fredriknk/ssense/PICTURES/IMG_8660.JPEG

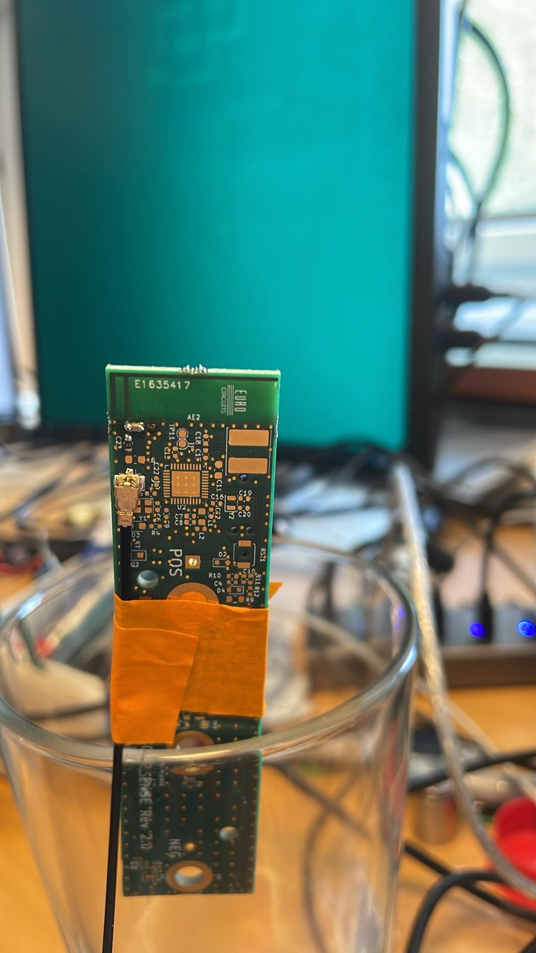
PICTURES/IMG_8660.JPEG
